edgarszaicevs/Cube-Logic/Arduino/ubloxgps.h

#ifndef UBLOXGPS_H
#define UBLOXGPS_H

#include <SoftwareSerial.h>

SoftwareSerial serial(13, 15, false, 256); // Connect the GPS RX/TX to Wemos pins D7 and D8
//#define serial Serial

const unsigned char UBX_HEADER[]        = { 0xB5, 0x62 };
const unsigned char NAV_PVT_HEADER[]    = { 0x01, 0x07 };
const unsigned char NAV_POSLLH_HEADER[] = { 0x01, 0x02 };
const unsigned char NAV_STATUS_HEADER[] = { 0x01, 0x03 };

enum _ubxMsgType {
  MT_NONE,
  MT_NAV_PVT,
  MT_NAV_POSLLH,
  MT_NAV_STATUS
};

const char UBLOX_INIT[] PROGMEM = {
  // Disable NMEA
  0xB5, 0x62, 0x06, 0x01, 0x08, 0x00, 0xF0, 0x00, 0x00, 0x00, 0x00, 0x00, 0x00, 0x01, 0x00, 0x24, // GxGGA off
  0xB5, 0x62, 0x06, 0x01, 0x08, 0x00, 0xF0, 0x01, 0x00, 0x00, 0x00, 0x00, 0x00, 0x01, 0x01, 0x2B, // GxGLL off
  0xB5, 0x62, 0x06, 0x01, 0x08, 0x00, 0xF0, 0x02, 0x00, 0x00, 0x00, 0x00, 0x00, 0x01, 0x02, 0x32, // GxGSA off
  0xB5, 0x62, 0x06, 0x01, 0x08, 0x00, 0xF0, 0x03, 0x00, 0x00, 0x00, 0x00, 0x00, 0x01, 0x03, 0x39, // GxGSV off
  0xB5, 0x62, 0x06, 0x01, 0x08, 0x00, 0xF0, 0x04, 0x00, 0x00, 0x00, 0x00, 0x00, 0x01, 0x04, 0x40, // GxRMC off
  0xB5, 0x62, 0x06, 0x01, 0x08, 0x00, 0xF0, 0x05, 0x00, 0x00, 0x00, 0x00, 0x00, 0x01, 0x05, 0x47, // GxVTG off

  // Disable UBX
  0xB5, 0x62, 0x06, 0x01, 0x08, 0x00, 0x01, 0x07, 0x00, 0x00, 0x00, 0x00, 0x00, 0x00, 0x17, 0xDC, // NAV-PVT off
  0xB5, 0x62, 0x06, 0x01, 0x08, 0x00, 0x01, 0x02, 0x00, 0x00, 0x00, 0x00, 0x00, 0x00, 0x12, 0xB9, // NAV-POSLLH off
  0xB5, 0x62, 0x06, 0x01, 0x08, 0x00, 0x01, 0x03, 0x00, 0x00, 0x00, 0x00, 0x00, 0x00, 0x13, 0xC0, // NAV-STATUS off

  // Enable UBX
  0xB5, 0x62, 0x06, 0x01, 0x08, 0x00, 0x01, 0x07, 0x00, 0x01, 0x00, 0x00, 0x00, 0x00, 0x18, 0xE1,   // NAV-PVT on
  //0xB5, 0x62, 0x06, 0x01, 0x08, 0x00, 0x01, 0x02, 0x00, 0x01, 0x00, 0x00, 0x00, 0x00, 0x13, 0xBE, // NAV-POSLLH on
  //0xB5, 0x62, 0x06, 0x01, 0x08, 0x00, 0x01, 0x03, 0x00, 0x01, 0x00, 0x00, 0x00, 0x00, 0x14, 0xC5, // NAV-STATUS on

  // Rate
  //0xB5, 0x62, 0x06, 0x08, 0x06, 0x00, 0x32, 0x00, 0x01, 0x00, 0x01, 0x00, 0x48, 0xE6, // 20Hz (50Ms)
  0xB5, 0x62, 0x06, 0x08, 0x06, 0x00, 0x3C, 0x00, 0x01, 0x00, 0x01, 0x00, 0x52, 0x22,   // 16.67Hz (60Ms)
  //0xB5, 0x62, 0x06, 0x08, 0x06, 0x00, 0x50, 0x00, 0x01, 0x00, 0x01, 0x00, 0x66, 0x9A, // 12.5Hz (80Ms)
  //0xB5, 0x62, 0x06, 0x08, 0x06, 0x00, 0x64, 0x00, 0x01, 0x00, 0x01, 0x00, 0x7A, 0x12, // 10Hz (100Ms)
  //0xB5, 0x62, 0x06, 0x08, 0x06, 0x00, 0xC8, 0x00, 0x01, 0x00, 0x01, 0x00, 0xDE, 0x6A, // 5Hz (500Ms)
  //0xB5, 0x62, 0x06, 0x08, 0x06, 0x00, 0xE8, 0x03, 0x01, 0x00, 0x01, 0x00, 0x01, 0x39, // 1Hz (1000Ms)

  // Фиксация минимум 5 спутников оставляем включенным только gps и sbas
  0xB5, 0x62, 0x06, 0x3E, 0x24, 0x00, 0x00, 0x00, 0x16, 0x04, 0x00, 0x05, 0xFF, 0x00, 0x01, 0x00, 0x00, 0x01, 0x01, 0x01, 0x03, 0x00, 0x01, 0x00, 0x00, 0x01, 0x05, 0x00, 0x03, 0x00, 0x00, 0x00, 0x00, 0x01, 0x06, 0x08, 0xFF, 0x00, 0x00, 0x00, 0x00, 0x01, 0xA6, 0x58,

  // Фиксация только 3d и автомобильный режим
  0xB5, 0x62, 0x06, 0x24, 0x24, 0x00, 0xFF, 0xFF, 0x04, 0x02, 0x00, 0x00, 0x00, 0x00, 0x10, 0x27, 0x00, 0x00, 0x05, 0x00, 0xFA, 0x00, 0xFA, 0x00, 0x64, 0x00, 0x2C, 0x01, 0x00, 0x3C, 0x00, 0x00, 0x00, 0x00, 0x00, 0x00, 0x00, 0x00, 0x00, 0x00, 0x00, 0x00, 0x4F, 0x83,

  // Sbas autoscan
  0xB5, 0x62, 0x06, 0x16, 0x08, 0x00, 0x01, 0x03, 0x03, 0x00, 0x00, 0x00, 0x00, 0x00, 0x2B, 0xB9,
};

struct NAV_PVT {
  unsigned char cls;
  unsigned char id;
  unsigned short len;
  unsigned long iTOW;          // GPS time of week of the navigation epoch (ms)
  unsigned short year;         // Year (UTC)
  unsigned char month;         // Month, range 1..12 (UTC)
  unsigned char day;           // Day of month, range 1..31 (UTC)
  unsigned char hour;          // Hour of day, range 0..23 (UTC)
  unsigned char minute;        // Minute of hour, range 0..59 (UTC)
  unsigned char second;        // Seconds of minute, range 0..60 (UTC)
  char valid;                  // Validity Flags (see graphic below)
  unsigned long tAcc;          // Time accuracy estimate (UTC) (ns)
  long nano;                   // Fraction of second, range -1e9 .. 1e9 (UTC) (ns)
  unsigned char fixType;       // GNSSfix Type, range 0..5
  char flags;                  // Fix Status Flags
  unsigned char reserved1;     // reserved
  unsigned char numSV;         // Number of satellites used in Nav Solution
  long lon;                    // Longitude (deg)
  long lat;                    // Latitude (deg)
  long height;                 // Height above Ellipsoid (mm)
  long hMSL;                   // Height above mean sea level (mm)
  unsigned long hAcc;          // Horizontal Accuracy Estimate (mm)
  unsigned long vAcc;          // Vertical Accuracy Estimate (mm)
  long velN;                   // NED north velocity (mm/s)
  long velE;                   // NED east velocity (mm/s)
  long velD;                   // NED down velocity (mm/s)
  long gSpeed;                 // Ground Speed (2-D) (mm/s)
  long heading;                // Heading of motion 2-D (deg)
  unsigned long sAcc;          // Speed Accuracy Estimate
  unsigned long headingAcc;    // Heading Accuracy Estimate
  unsigned short pDOP;         // Position dilution of precision
  short reserved2;             // Reserved
  unsigned long reserved3;     // Reserved
};

//NAV_PVT pvt;

struct NAV_POSLLH {
  unsigned char cls;
  unsigned char id;
  unsigned short len;
  unsigned long iTOW; // GPS time of week of the navigation epoch (ms)
  long lon;
  long lat;
  long height;
  long hMSL;
  unsigned long hAcc;
  unsigned long vAcc;
};

struct NAV_STATUS {
  unsigned char cls;
  unsigned char id;
  unsigned short len;
  unsigned long iTOW;
  unsigned char gpsFix;
  char flags;
  char fixStat;
  char flags2;
  unsigned long ttff;
  unsigned long msss;
};

union UBXMessage {
  NAV_PVT navPvt;
  NAV_POSLLH navPosllh;
  NAV_STATUS navStatus;
};

UBXMessage ubxMessage;

// The last two bytes of the message is a checksum value, used to confirm that the received payload is valid.
// The procedure used to calculate this is given as pseudo-code in the uBlox manual.
void calcChecksum(unsigned char* CK, int msgSize) {
  memset(CK, 0, 2);
  for (int i = 0; i < msgSize; i++) {
    CK[0] += ((unsigned char*)(&ubxMessage))[i];
    CK[1] += CK[0];
  }
}

// Compares the first two bytes of the ubxMessage struct with a specific message header.
// Returns true if the two bytes match.
boolean compareMsgHeader(const unsigned char* msgHeader) {
  unsigned char* ptr = (unsigned char*)(&ubxMessage);
  return ptr[0] == msgHeader[0] && ptr[1] == msgHeader[1];
}

void gpsSetup() {
  // send configuration data in UBX protocol
  for (int i = 0; i < sizeof(UBLOX_INIT); i++) {
    serial.write( pgm_read_byte(UBLOX_INIT + i) );
    delay(5); // simulating a 38400baud pace (or less), otherwise commands are not accepted by the device.
  }
}

// Reads in bytes from the GPS module and checks to see if a valid message has been constructed.
// Returns the type of the message found if successful, or MT_NONE if no message was found.
// After a successful return the contents of the ubxMessage union will be valid, for the
// message type that was found. Note that further calls to this function can invalidate the
// message content, so you must use the obtained values before calling this function again.
int processGPS() {
  static int fpos = 0;
  static unsigned char checksum[2];
  static byte currentMsgType = MT_NONE;
  static int payloadSize = sizeof(UBXMessage);

  while ( serial.available() ) {

    byte c = serial.read();
    //Serial.write(c);

    if ( fpos < 2 ) {
      // For the first two bytes we are simply looking for a match with the UBX header bytes (0xB5,0x62)
      if ( c == UBX_HEADER[fpos] )
        fpos++;
      else
        fpos = 0; // Reset to beginning state.
    } else {
      // If we come here then fpos >= 2, which means we have found a match with the UBX_HEADER
      // and we are now reading in the bytes that make up the payload.

      // Place the incoming byte into the ubxMessage struct. The position is fpos-2 because
      // the struct does not include the initial two-byte header (UBX_HEADER).
      if ( (fpos - 2) < payloadSize )
        ((unsigned char*)(&ubxMessage))[fpos - 2] = c;

      fpos++;

      if ( fpos == 4 ) {
        // We have just received the second byte of the message type header,
        // so now we can check to see what kind of message it is.
        if ( compareMsgHeader(NAV_PVT_HEADER) ) {
          currentMsgType = MT_NAV_PVT;
          payloadSize = sizeof(NAV_PVT);
        } else if ( compareMsgHeader(NAV_POSLLH_HEADER) ) {
          currentMsgType = MT_NAV_POSLLH;
          payloadSize = sizeof(NAV_POSLLH);
        } else if ( compareMsgHeader(NAV_STATUS_HEADER) ) {
          currentMsgType = MT_NAV_STATUS;
          payloadSize = sizeof(NAV_STATUS);
        } else {
          // unknown message type, bail
          fpos = 0;
          continue;
        }
      }

      if ( fpos == (payloadSize + 2) ) {
        // All payload bytes have now been received, so we can calculate the
        // expected checksum value to compare with the next two incoming bytes.
        calcChecksum(checksum, payloadSize);
      } else if ( fpos == (payloadSize + 3) ) {
        // First byte after the payload, ie. first byte of the checksum.
        // Does it match the first byte of the checksum we calculated?
        if ( c != checksum[0] ) {
          // Checksum doesn't match, reset to beginning state and try again.
          fpos = 0;
        }
      } else if ( fpos == (payloadSize + 4) ) {
        // Second byte after the payload, ie. second byte of the checksum.
        // Does it match the second byte of the checksum we calculated?
        fpos = 0; // We will reset the state regardless of whether the checksum matches.
        if ( c == checksum[1] ) {
          // Checksum matches, we have a valid message.
          return currentMsgType;
        }
      } else if ( fpos > (payloadSize + 4) ) {
        // We have now read more bytes than both the expected payload and checksum
        // together, so something went wrong. Reset to beginning state and try again.
        fpos = 0;
      }
    }
  }
  return MT_NONE;
}

#endif
